Squantor/PPG_sensor_research/software/common/src/stream_uart.cpp

/*
MIT License

Copyright (c) 2019 Bart Bilos

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
THE SOFTWARE IS PROVIDED "AS IS", WITHOUT WARRANTY OF ANY KIND, EXPRESS OR
IMPLIED, INCLUDING BUT NOT LIMITED TO THE WARRANTIES OF MERCHANTABILITY,
FITNESS FOR A PARTICULAR PURPOSE AND NONINFRINGEMENT. IN NO EVENT SHALL THE
AUTHORS OR COPYRIGHT HOLDERS BE LIABLE FOR ANY CLAIM, DAMAGES OR OTHER
LIABILITY, WHETHER IN AN ACTION OF CONTRACT, TORT OR OTHERWISE, ARISING FROM,
OUT OF OR IN CONNECTION WITH THE SOFTWARE OR THE USE OR OTHER DEALINGS IN THE
SOFTWARE.
*/
/*
Datastream that points to the user facing UART interface
*/

#include <results.h>
#include <stream_uart.hpp>
#include <PPG_sensor_V000.hpp>
#include <mcu_ll.h>

const static char streamUartName[] = "uartStream";
result writeUart(const char *c);
result readUart(char *c);
const datastreamChar_t streamUart = {writeUart, readUart, streamUartName};

result writeUart(const char *c)
{
    while((UartGetStatus(UART_DEBUG) & UART_STAT_TXRDY) == 0) 
        ;
    UartSendByte(UART_DEBUG, *c);
    return noError;
}

result readUart(char *c)
{
    if((UartGetStatus(UART_DEBUG) & UART_STAT_RXRDY) != 0)
    {
        *c = UartReadByte(UART_DEBUG);
        return noError;
    }
    else
        return streamEmtpy;       
}
